MacNite/HiveHub/docs/hiveinside-ble-sensor.md

# HiveInside in-hive BLE sensor

**HiveInside** is an in-hive node that runs its vibration and acoustic FFTs on
board and broadcasts the finished results, so the HiveHub only has to scan for it
— no wiring into the hive. It supplies full FFT bands the wired sensors cannot,
and its temperature/humidity can replace the wired DS18B20/SHT4x for that hive.

HiveInside is the **XIAO nRF54LM20A Sense** node. It emits a 29-byte
manufacturer-data frame that a current HiveHub decodes out of the box:

| Board | How it is read | Advertising | OTA image |
|---|---|---|---|
| **HiveInside (nRF54LM20A)** | passive **beacon** scan (one shared window per cycle) | **always on**, no pairing window | signed Zephyr / MCUboot image (`zephyr.signed.bin`, a few hundred KB) |

> The earlier **ESP32-C6 HiveInside prototype** (which served the same frame over
> GATT and took a >1 MB ESP32 OTA image) has been **removed from the ecosystem**.
> HiveInside now unambiguously means the nRF54LM20A beacon node; there is no
> ESP32-C6 pairing type, GATT measurement path, or C6 firmware target anymore.

The frame carries (little-endian; valid only when the matching **flags** bit is
set — a failed on-board sensor is reported as *absent*, never as `0.0`):

| Group (flags bit) | Fields | HiveHub field |
|---|---|---|
| SHT (bit 0) | temperature, humidity | `hive_{n}_temp_c`, `ble_{n}_humidity_percent` |
| accel (bit 1) | RMS + peak + swarm/fanning/activity bands | `accel_{n}_*` (reused accelerometer fields; see the note on capture diagnostics below) |
| mic (bit 2) | RMS + peak + 5 acoustic bands | `hives[].mic.*`, read back as `mic_{n}_*` |
| battery (bit 3) | percent, millivolts | `ble_{n}_battery_percent`, `ble_{n}_battery_mv` |

The two broadband **peak** values (`accel_{n}_peak_mg`, `mic_{n}_peak_dbfs`)
arrived with **frame version 2** — appended after the version-1 fields, none of
which moved. HiveHub gates on the received frame length rather than the version
byte, so a node still on version 1 keeps decoding in full and simply reports no
peaks; the dashboard then falls back to the broadband RMS it always showed.

A [sample frame + reference decoder](../test-data/hiveinside_nrf54_beacon.py)
lives in `test-data/` (`python3 hiveinside_nrf54_beacon.py`).

Beyond the beacon, a HiveInside is the only device on a hub with a microphone
you can actually listen to: node firmware 0.6.2+ and hub firmware 0.30.0+ can
record 10–60 seconds from inside the hive on request and relay it here. That is
a connected, authenticated session rather than a passive scan, so it is covered
separately in [Listening to a hive](audio-recording.md).

---

## Pairing

1. **Firmware flag.** Set `ENABLE_BLE_SCAN 1` (the same shared passive scan used
   for HolyIot / RuuviTag). The nRF54 node is beacon-only, so no GATT measurement
   flag is needed. (`HIVEINSIDE_OTA_ENABLED`, default 1, compiles in the BLE OTA
   relay described below.)
2. **Pair from the setup portal.** Open the provisioning portal (press the setup
   button, or use **Start AP mode** in the dashboard, then join the
   `HiveHub-Setup-XXXX` AP), scan for BLE devices, and
   press **➕ Add BLE in-hive sensor** on the hive. Choose the sensor type
   **HiveInside (nRF54LM20A) — beacon** and enter/copy the node's MAC — picking
   the node from the scan dropdown selects the type for you. This is the hive's
   beacon lane, so it does not block a HiveTraffic bee counter or a HiveHeart on
   the same hive; it is exclusive only with the other beacon formats and with a
   wired DS18B20.

> The nRF54 node has **no pairing window** — it is always discoverable, so there
> is nothing to long-press before scanning. Its button just forces an immediate
> measurement.

The same choice is available in the
[web configurator](https://macnite.github.io/HiveHub/configurator.html), which
emits the matching `HIVE_i_JSON` pre-seed and firmware flags.

---

## Firmware updates (OTA relay)

The HiveHub is the only Wi-Fi node, so it **relays** a HiveInside image over BLE
GATT (streamed straight from the HTTPS download into the node's OTA
characteristics; the CRC-32 is verified end-to-end before the node swaps slots).
The relayed bytes are an nRF54 MCUboot image and are forwarded **opaquely** — the
HiveHub never runs its own ESP32 self-OTA architecture guard on them; only the
node verifies its own image. The relay locates the node by its identity address
(learned from this cycle's measurement scan) before connecting.

> The node advertises **connectable** (`ADV_IND`) continuously — it does not open
> an OTA window on demand, and this page previously said it was a
> "non-connectable beacon", which was never true of any shipped firmware. The
> measurement frame is still read passively out of the advertisement; being
> connectable is what lets the OTA relay and an audio session reach it at all.
> It also means the node's OTA GATT service is reachable by any BLE central in
> range, so the signing key MCUboot verifies against is the only thing standing
> between a stranger and the contents of slot 1 — build releases with your own
> key, not the SDK development key.

Uploads are **board-stamped** `nrf54lm20a` (the only HiveInside board). In the
dashboard firmware tool the target and version are filled in from the filename as
soon as the `.bin` is picked: HiveInside's build names its artifact
`hiveinside-nrf54lm20a-v0.4.7-lowpower.signed.bin` (see HiveInside's
[`docs/ota-over-ble.md`](https://github.com/MacNite/HiveInside/blob/main/docs/ota-over-ble.md)),
and the form reads `HiveInside` and `0.4.7` straight out of it — the build variant
(`bringup` / `lowpower`) and the `.signed` suffix are not part of the version. The
form says underneath the file picker what it recognized, and nothing is guessed for
a name it does not recognize: the target stays on whatever is selected and the
version field is left alone. The **Board** field then shows
`HiveInside (nRF54LM20A)` **disabled** — there is nothing to choose, and the
release is always stamped `nrf54lm20a`. The older
`hiveinside_nrf54lm20a_1.0.0.bin` naming is detected the same way. The
API still accepts an omitted board (legacy `board = NULL` releases), but the server
refuses a release whose declared board disagrees with its filename. A HiveInside release now
unambiguously means an nRF54 image, so no per-board matching is done — the latest
active HiveInside release (nrf54lm20a-stamped or a legacy board-agnostic one) is
relayed.

### Triggering a relay

Uploading a `.bin` only **registers** a release — nothing starts the transfer,
on any check-in. The relay is queued explicitly, either from the built-in
dashboard or over the API.

From the dashboard: **Device & admin → Firmware → HiveInside nodes**, then
**Relay to node** on the row for the hive you want to update. The button appears
only when the uploaded release would actually be accepted (see the guards
below), and requires an admin login.

The row then shows the relay's state — *relay queued*, *relaying…*, or *relay
failed* with the reason spelled out underneath (e.g. `HiveInside not found in
scan (asleep or out of range?)`). The button is disabled while a relay is
already queued or running, so a second click cannot stack a duplicate transfer.
A relay that succeeds leaves no badge: the node's advertised version changing is
the confirmation.

> Firmware downloads are deliberately excluded from response compression
> (`SelectiveGZipMiddleware`). A gzipped response has no `Content-Length`, and
> the ESP32 sizes its download from that header — compressing `/firmware/*` made
> every relay fail with `invalid firmware content length -1` before it opened a
> BLE session. Keep any reverse proxy in front of the API from re-compressing
> that path for the same reason.

Over the API:

```bash
curl -X POST -H "X-API-Key: $API_KEY" \
  "https://<host>/api/v1/devices/<device_id>/commands/update-hiveinside?slot=<hive>"
```

`slot` is the **hive index**, so any hive can be updated (up to `MAX_HIVES`), and
the HiveHub matches only HiveInside pairings when resolving the MAC. The relay
runs on the HiveHub's next upload cycle — about 10 minutes by default, or
whatever send interval the device is configured for. There is no separate
command poll; a command is picked up once per cycle, in every mode.

A relay that is claimed but never reported on (the HiveHub crashed, or simply
lost the fire-and-forget result POST after a multi-minute BLE transfer) is
swept back onto the queue after `STALE_CLAIM_MINUTES`, up to
`MAX_COMMAND_ATTEMPTS` times, and then failed with `timed out: claimed by the
device N time(s) without reporting a result`. Only relays are retried this way;
destructive commands such as `factory_reset` fail on the first timeout rather
than being silently repeated.

A hub that *resets* mid-relay no longer has to wait that out. It records the
command id in RTC memory before starting, and the next boot reports the attempt
explicitly — `hub reset during relay (panic/exception) — firmware transfer did
not complete` — against the still-open row. That closes the command on the first
cycle after the reset instead of an hour and three attempts later, and it names
the reset reason, so a crashing hub is distinguishable from one that is merely
out of range. The command is then genuinely failed rather than retried: re-queue
it yourself once the hub is healthy.

Two guards apply before the command is queued:

| Condition | Result |
|---|---|
| `slot` outside `1..18` | `400` |
| No active `hiveinside` release | `404` |
| Release not newer than the version the node advertises | `409` |

The version gate compares against `hives[].ble.firmware_version` — the version
the node itself broadcasts — so re-running the command after a successful update
is a no-op instead of a pointless multi-minute BLE transfer and a reboot of a
healthy hive sensor. A node that has never advertised a version is not gated.
Pass `force=true` to relay regardless, which is what you want after a reverted or
interrupted update where the node still runs the old image.

> **How the board/version are learned.** The nRF54 beacon advertises its board and
> firmware version in a second manufacturer-data element in its **scan response**
> (magic `'I'`), distinct from the 29-byte measurement frame (magic `'H'`). The
> HiveHub active-scans by default, so both arrive together — no GATT connection is
> needed to learn them, and the HiveHub forwards the node's `board`/`fw` fields to
> the backend.

> **nRF54 / MCUboot semantics:** the signed Zephyr image is small (transfer is
> quick), and after the relay completes the node reboots into a *test* image and
> confirms it. A reverted (unconfirmed) update silently keeps the old firmware,
> so verify the node's reported `fw` version after an update.

The dashboard shows that version in two places on **Device & admin**: the
**Status** card's *In-hive sensors* list (every paired wireless node, with the
version for the ones that advertise one — only HiveInside does), and
**Firmware → HiveInside nodes**: one row per hive whose node was heard, with the
advertised version and board (e.g. `v0.4.0 · nrf54lm20a`). The section only appears once a HiveInside
node has actually reported, and it keeps the last known identity when a node
misses a scan window, so it reads as "what this node is running", not "what was
in the last packet".

Each row in **Firmware → HiveInside nodes** is headed by the *hive* name, which
says where the node sits and nothing about which unit it is. The **?** beside
that name names the node itself: the local name it advertises and the BLE
address it is paired on. HiveInside firmware from **0.5.0** advertises
`HiveInside-XXXX`, where the four hex digits are the last two bytes of the
node's address — earlier firmware advertised a bare `HiveInside` on every node,
so for those the address is all there is to tell two of them apart. Both fields
ride in `hives[].ble.device_name` and `hives[].ble.mac` (raw JSON, no column),
and the HiveHub sends the address whether or not the node answered a scan.

### Diagnosing a failed relay

Watch the HiveHub's serial console at 115200 across an attempt. A healthy relay
prints, in order:

```
[CMD] Received command 20: update_hiveinside
[HI-OTA] Downloading HiveInside firmware: https://…/hiveinside-….signed.bin
[HEAP] relay-start: free=… largest=… min_ever=…
[HI-OTA] Download open: 1093632 bytes; bringing up BLE
[HEAP] relay-download-open: free=… largest=… min_ever=…
[HI-OTA] connecting to … 
[HI-OTA] connected: MTU=247 chunk=244 image=1093632 bytes crc=0x…
[HI-OTA] relayed 32768/1093632 bytes            ← every 32 KB
[HI-OTA] device reports DONE — it will reboot into the new image
[HI-OTA] result: OK
```

Where it stops, and what it says, maps to a cause:

* **`MTU=23 chunk=20`** — MTU negotiation did not take. The transfer still works
  but runs roughly ten times longer, which makes every other timeout tighter.
* **`DATA write failed …`** — the relay now asks the node *why* instead of
  guessing. `STATUS unreadable — link is down` is a genuine radio/link loss;
  `device rejected the stream: state=0x… (…)` means the node refused the bytes
  (CRC, size, flash write, wrong state) and the transfer never had a chance. The
  same distinction reaches the dashboard, so the row's reason is now the node's
  own verdict rather than "BLE link lost?" for all of them.
* **`… flash write failed (errno -116)`** — the trailing errno is the node's own
  `rc` from the failed flash operation, read from the seventh STATUS byte
  (HiveInside 0.4.7+, 0.24.13+ on this side). It exists because the `lowpower`
  HiveInside image has no console, so `state=0x12` was otherwise the entire
  diagnosis available in the field — and six error codes cannot separate a slot
  that is too small (`-EINVAL`) from a radio timeslot that never arrived
  (`-ETIMEDOUT`). Older nodes send six bytes and no suffix appears.
* **`[HEAP] *** CORRUPTION DETECTED at stage: … ***`** — the allocator's own
  structures are damaged. The named stage is the one that did it; everything
  after that point in the boot is unreliable, including any crash that follows.
* **`[BLE] … address type … known from this boot's scan`** — the normal path
  since 0.24.12. The relay reuses what the measurement scan already learned
  instead of running a second scan of its own; see the note below.
* **`[BLE] refusing to scan: the scan singleton belongs to port lifetime …`** —
  the safety net described below fired. Not a fault; the relay reports a clean
  failure rather than crashing.
* **A boot banner instead of a result line** — the hub reset mid-relay. Read
  `Reset reason:` on the line after the wake reason: `panic/exception` means a
  crash, with the Guru Meditation dump immediately above it.

A panic dump decodes in place when the console is `pio device monitor` (both
environments set `monitor_filters = esp32_exception_decoder`). For a dump
captured elsewhere, feed the addresses to `addr2line` against the exact image
that is flashed — `rename_firmware.py` names it `hivehub_<board>_<version>.elf`,
and `firmware/ci/package_build.sh` copies it into `firmware/dist/`:

```bash
riscv32-esp-elf-addr2line -pfiaC \
  -e firmware/dist/hivehub_esp32-c6_<version>.elf 0x… 0x… 0x…
```

The dump's trailing `ELF file SHA256:` must match that file, or the decoded
names are fiction.

> **Why the relay no longer scans (0.24.12+).** `NimBLEScan` initialises its
> scan-response timer once, in its constructor, against whichever porting layer
> is up at that moment. `NimBLEDevice::deinit()` tears the porting layer down
> *before* it would delete that singleton, so `deinit(true)` faults inside
> `~NimBLEScan()` — and `deinit(false)`, the workaround, leaves the singleton
> holding a callout belonging to a porting layer that no longer exists. Scan
> again later in the same boot and the first `ble_npl_callout_stop()` hands a
> freed handle to `esp_timer_stop()`: `Load access fault`, `MEPC` in
> `esp_timer.c:257`. That is exactly what killed a relay in the field — the
> measurement scan ran, the stack was cycled for the WiFi upload, and the
> relay's own 4-second locate scan ran in the second port lifetime.
>
> The relay now takes the address type from the measurement scan that already
> ran this cycle, so it never scans at all. `src/ble_stack.h` owns the stack's
> lifetime for every caller and refuses a scan that would land in the wrong port
> lifetime, so the remaining callers fail loudly instead of faulting.
>
> One consequence worth knowing: the setup portal's **discovery scan** is the
> one caller that legitimately wants to scan late in a boot. It declines with a
> log line instead of crashing — which, in 0.25.3, is what made a remotely
> opened AP list **no BLE devices at all** on any hub that already had a sensor
> paired: the AP came up, the radio was fine, and the scan simply never ran.
>
> Firmware **0.25.5** closes that (0.25.4 tried, but parked the request in a
> `RTC_DATA_ATTR` variable the bootloader wipes on the way back up): a `start_provisioning` command that would
> land in a spent port lifetime parks the request in RTC memory and reboots, so
> the portal opens before the first measurement cycle — where the scan is
> allowed — exactly as a button press does. Nothing is needed from the user
> beyond noticing the extra reboot. If a portal ever does come up without a
> scan, it now says so on the page instead of showing an empty list.

See [api.md](api.md) for the `update-hiveinside` command and payload.
