MacNite/HiveHub/docs/holyiot-ble-sensor.md

# HolyIot 25015 in-hive BLE sensor

HiveHub can read up to **two HolyIot 25015 BLE sensors** — one per hive — as
optional in-hive sensors. The ESP32 acts as a passive **BLE bridge**: no wiring
into the hive, just a battery beacon sitting on/near the comb that the logger
scans for once per upload cycle.

The 25015 (nRF54L15) carries three sensors:

| On-board chip | Measures | HiveHub field |
|---|---|---|
| SHT40 | temperature | `hive_{1,2}_temp_c` (shared with / replacing the wired DS18B20) |
| SHT40 | relative humidity | `ble_{1,2}_humidity_percent` |
| LPS22HB | barometric pressure | `ble_{1,2}_pressure_hpa` |
| LIS2DH12 | 3-axis acceleration | `accel_{1,2}_*` (reused accelerometer fields) |

It replaces the previous wired LIS3DH/LIS2DH12 accelerometer
([accelerometer.md](accelerometer.md)).

---

## Enabling and pairing

1. **Firmware flag.** Set `ENABLE_BLE_SCAN 1` in `secrets.h` (see
   `secrets.example.h` for all options). The wired in-hive microphone
   (`ENABLE_INMP441_MICS`) and DS18B20 probes (`ENABLE_DS18B20_HIVE_TEMP`) are
   independent optional features — turn them off if a build relies on the BLE
   sensor instead.
2. **Pair from the setup portal.** Open the provisioning portal (short-press the
   setup button, join the `HiveHub-Setup-XXXX` AP, browse to
   `http://192.168.4.1/`). Under **Wireless sensors**:
   - Click **scan for wireless sensors** to list advertising BLE devices; sensors
     carrying a parseable 25015 payload are flagged.
   - Click **➕ Add wireless sensor**, leave the type as an in-hive sensor
     (e.g. **HolyIot 25015**), pick **Hive 1** or **Hive 2** in the **Maps to**
     dropdown, paste the sensor's MAC, then **Save and reboot**. The **Maps to**
     choice — not the row order — decides the hive, so you can pair a wireless
     sensor for hive 2 alone and leave hive 1 on its wired probe.
   The MACs persist in Preferences (`ble_mac0` = hive 1, `ble_mac1` = hive 2).

Each cycle the firmware scans for `HOLYIOT_BLE_SCAN_SECONDS` (default 6 s),
matches advertisements to the paired MACs, and folds the readings into the
normal measurement upload before connecting WiFi.

### Hive temperature source

When `ENABLE_DS18B20_HIVE_TEMP` is on **and** the wired probe returns a valid
reading, the DS18B20 wins and the BLE temperature is the fallback. With the
DS18B20 disabled, `hive_{1,2}_temp_c` comes from the paired sensor's SHT40.

---

## Advertisement format — confirmed June 2026

The 25015 (HY-25015, P6-B Pro, firmware V1.0.0) broadcasts **four simultaneous
advertisement slots**, each cycling at ~500 ms. All use company ID `0xFFFF` in
the manufacturer-specific AD (type `0xFF`). The slot type is identified by the
**frame-type byte** at offset 2 (first byte after the 2-byte company ID):

| Frame | Type byte | Payload (offsets within manufacturer data) |
|---|---|---|
| T&H | `0x0A` | d[3..4] temp int16 BE /10 → °C; d[5..6] humidity uint16 BE /10 → %RH |
| Accel | `0x0B` | d[3..4] X int16 BE mg; d[5..6] Y int16 BE mg; d[7..8] Z int16 BE mg |
| Baro | `0x0C` | d[3..5] pressure uint24 BE Pa; ×0.01 → hPa |
| iBeacon | `0x02` | Static Major/Minor proximity identifiers — **no sensor data** |

Battery percentage comes from the **Service Data** (UUID `0x180A`, 9 bytes):
`[frame_type][MAC 6 B][TX power][battery %]` — last byte.

The firmware decoder (`firmware/src/ble_sensor.cpp`) merges all three sensor
frames into a single snapshot per scan cycle. All confirmed against real packet
captures (nRF Connect) with simultaneous live readings from the companion app.

---

## Acceleration & the low-rate pre-swarm insight

A passive beacon emits **periodic single-shot** acceleration samples, not a
high-rate stream, so the 8–30 Hz FFT swarm band the wired sensor produced cannot
be computed. Instead:

- The firmware reports a **per-cycle AC magnitude** (gravity removed) in the
  reused `accel_{1,2}_rms_mg` / `accel_{1,2}_peak_mg` fields
  (`accel_{1,2}_band_*_mg` stay null). Raw per-axis values, battery % and link
  RSSI are kept in `raw_json` (`ble_{1,2}_accel_*_mg`,
  `ble_{1,2}_battery_percent`, `ble_{1,2}_rssi_dbm`).
- The server runs `detect_lowrate_accel_swarm` (insights.py): it trends the
  **night-time mean** of `accel_{1,2}_rms_mg` and raises a lower-confidence
  `swarm` / `watch` alert (`swarm-ble-vibration-chN`) when in-hive movement
  climbs ≥ `LOWRATE_SWARM_RISE_MULT`× over its baseline. Rising comb excitation
  over several days can precede swarming (Bencsik/Ramsey). When real FFT-band
  data exists for a hive, this detector defers to the band detector to avoid a
  duplicate alert.

This is a coarser signal than research-grade comb vibrometry — the LIS2DH12's
noise floor limits it to detecting the louder, collective movement changes — but
it adds a genuine, no-wiring pre-swarm cue alongside the weight and temperature
rules.

---

## Database

Migration `008_holyiot_ble_sensor.sql` adds the four new columns
(`ble_{1,2}_humidity_percent`, `ble_{1,2}_pressure_hpa`). `init_db()` creates the
same columns on fresh deployments, and both are idempotent. Acceleration and
temperature reuse the existing `accel_{1,2}_*` and `hive_{1,2}_temp_c` columns.
