MacNite/HiveHub/firmware/include/hive_config.h

// hive_config.h — dynamic registry of up to MAX_HIVES hives and the sensors
// mapped to each one. Replaces the old fixed "hive 1 / hive 2" model.
//
// Each hive owns:
//   - one SCALE, backed by an HX711 (legacy pins), a NAU7802 I2C channel
//     (optionally behind a TCA9548A mux), or a paired beehivemonitoring.com
//     HiveScale GATT sensor;
//   - up to three in-hive BLE sensors, one per "lane" (see ble_lanes.h): one
//     beacon (HolyIot / RuuviTag / HiveInside), one HiveTraffic bee counter and
//     one HiveHeart. A wired DS18B20 temperature probe, addressed by its 1-Wire
//     ROM, occupies the beacon lane — probe and beacon both feed hives[].temp_c,
//     so a hive still takes one or the other, never both;
//
// The whole registry is persisted as one compact JSON blob per hive in NVS
// ("h0_cfg" .. "h17_cfg") plus a "hive_count" key, written by the provisioning
// portal (portal.cpp) and parsed back here at boot. Before that NVS key ever
// exists, a device instead seeds gHives from either up to MAX_HIVES HIVE_i_JSON
// secrets.h macros (same blob shape, see hive_config.cpp's seedHivesFromSecrets)
// or, absent those, migrates the legacy two-slot keys into a 2-hive registry —
// either way existing devices keep working without a portal visit.
#pragma once

#include <Arduino.h>
#include "config.h"
#include "ble_lanes.h"

namespace hivecfg {

// Which hardware drives a scale channel.
enum class ScaleBackend : uint8_t {
  None    = 0,
  HX711   = 1,   // legacy load-cell amp on a dedicated pin pair
  NAU7802 = 2,   // 24-bit I2C ADC (optionally behind a TCA9548A mux)
};

struct ScaleChannel {
  ScaleBackend backend = ScaleBackend::None;

  // HX711 backend: which of the two board HX711 instances (0 -> HX1_*, 1 -> HX2_*).
  uint8_t hxIndex = 0;

  // NAU7802 backend. The NAU7802's I2C address is FIXED at 0x2A (no
  // address-select pin), so it is not part of the configuration: the legacy
  // "addr" JSON field is parsed for backward compatibility, normalized to
  // NAU7802_I2C_ADDRESS (with a log when it differed) and no longer persisted
  // or presented as configurable.
  int8_t  muxChannel = -1;   // -1 = directly on the main bus; 0..7 behind the mux
  uint8_t adcChannel = 1;    // NAU7802 input mux: 1 -> CH1, 2 -> CH2

  // Calibration (raw -> kg), same convention as the HX711 path: kg = (raw-offset)/factor.
  long  offset = 0;
  float factor = -7050.0f;

  // Runtime-only (never persisted): set by validateRegistry() when this channel
  // is part of an invalid/conflicting topology (duplicate physical channel,
  // out-of-range mux/ADC, direct+muxed NAU7802 mix, implausible calibration).
  // A flagged channel is never operated — scalebus::readChannel() fails closed —
  // but the stored configuration is preserved so the portal can show and fix it.
  bool configError = false;

  bool valid() const { return backend != ScaleBackend::None && !configError; }
};

// One wireless pairing. `type` matches the portal vocabulary
// (holyiot|ruuvitag|hiveinside_nrf54|hiveheart|hivescale|beecounter). A `hivescale`
// pairing is a scale source; every other type is an in-hive BLE sensor, at most
// one per lane (blelanes::laneFor). `isGatt()` marks connection-based types that
// count against MAX_GATT_READS_PER_CYCLE.
struct BlePairing {
  String type;
  String mac;   // canonical "AA:BB:CC:DD:EE:FF"
  bool isGatt() const;
};

static const uint8_t MAX_SCALES_PER_HIVE = 1;
// One pairing per lane, so the ceilings come straight from ble_lanes.h: at most
// four stored pairings (a wireless HiveScale scale source + the three in-hive
// lanes), of which at most three are in-hive sensors. hiveFromJson() enforces
// this on every load AND on every portal save.
static const uint8_t MAX_BLE_PER_HIVE        = blelanes::LANE_COUNT;
static const uint8_t MAX_INHIVE_BLE_PER_HIVE = blelanes::INHIVE_LANE_COUNT;

struct Hive {
  uint8_t index = 0;          // 1..MAX_HIVES; 0 means "slot unused"
  String  name;

  uint8_t      scaleCount = 0;
  ScaleChannel scales[MAX_SCALES_PER_HIVE];

  bool    hasDsRom = false;   // a DS18B20 ROM is mapped to this hive
  uint8_t dsRom[8] = {0};     // 1-Wire ROM address

  uint8_t    bleCount = 0;
  BlePairing ble[MAX_BLE_PER_HIVE];

  bool used() const { return index >= 1; }
};

// The live registry. gHiveCount entries of gHives[] are populated (index 1..N).
extern Hive    gHives[MAX_HIVES];
extern uint8_t gHiveCount;

// Parse the NVS per-hive blobs (and hive_count) into gHives. When no blobs exist
// yet, migrate the legacy fixed-slot keys (scale offsets/factors, ble_mac0/1,
// wcount/wtypeN/wmacN/wslotN) into a two-hive registry so an upgraded device keeps
// working without re-provisioning. Always finishes with validateRegistry().
void loadHiveConfig();

// Authoritative validation of the loaded registry (runs on every load AND on
// every portal save — never rely on the portal page's dropdown behavior):
//   - duplicate or out-of-range hive indices  -> offending hives dropped;
//   - invalid mux (-1..7 only, no masking), invalid ADC channel (1/2), invalid
//     HX711 index, duplicate physical channels, direct+muxed NAU7802 mixes,
//     non-finite/implausible calibration factors -> offending channels get
//     configError set (never operated, preserved for correction in the portal);
//   - obsolete wired-BeeCounter "beecounter"-typed pairings without a BLE MAC
//     cannot exist (pairings are MAC-keyed), so nothing wired can activate.
// Every problem is logged with hive index + channel detail. Returns true when
// nothing had to be flagged or dropped.
bool validateRegistry();

// Serialize gHives back to NVS (used after a calibration writeback).
void saveHiveConfig();

// Serialize a single hive to its compact JSON blob string (used by the portal).
String hiveToJson(const Hive& h);
// Parse one hive blob into `out`; returns false on malformed input.
bool   hiveFromJson(const String& json, Hive& out);

// Convenience: total configured wired scale channels across all hives (<= MAX_SCALES).
uint8_t totalScaleChannels();

// MAC of the HiveInside node on the hive addressed by `slot`, or "" when that
// hive carries no HiveInside pairing. `slot` is the HIVE INDEX (1..MAX_HIVES),
// so every hive can be targeted by an OTA relay — not just the first two, which
// is all the legacy bleSensorMac0/1 globals could ever reach. A registry whose
// hives are not numbered 1..N falls back to registry position `slot - 1`, which
// is what the legacy globals addressed.
//
// Only HiveInside pairings are ever returned: the legacy globals held the first
// beacon of ANY type, so a hive whose first pairing was a HolyIot or RuuviTag
// pointed an OTA relay straight at the wrong device.
String hiveInsideMacForSlot(uint8_t slot);

// The paired HiveTraffic counter's MAC for hive index `slot`, or "" when that
// hive has no counter. Same index-then-position resolution as
// hiveInsideMacForSlot, matching only "beecounter" pairings. Used by the
// update_beecounter OTA relay; the measurement path walks the registry itself
// (bee_counter_client.cpp::bleRunCycleRegistry) rather than going slot by slot.
String beeCounterMacForSlot(uint8_t slot);

// Format/parse a DS18B20 ROM as 16 hex chars ("28FF64...") for the portal/NVS.
String   romToHex(const uint8_t rom[8]);
bool     romFromHex(const String& hex, uint8_t rom[8]);

}  // namespace hivecfg
