MacNite/HiveHub/firmware/include/bee_counter_client.h

// bee_counter_client.h — HiveTraffic entrance bee counter, BLE/GATT ONLY.
//
// The wired I2C BeeCounter path (its fixed slave addresses, register map,
// latch/reset command, snapshot retries, and firmware-over-the-wire updates)
// was removed: BLE/GATT is the only supported BeeCounter transport. Once per
// upload cycle the firmware connects
// to each paired HiveTraffic MAC, reads one JSON measurement characteristic —
// LIFETIME totals only — and disconnects. The backend differences consecutive
// totals into per-interval counts, so no latch/reset command exists.
//
// Firmware updates run over GATT as well: the backend queues an
// `update_beecounter` command and HiveHub streams the image into the counter's
// OTA characteristics (see gatt_ota.h and hivehub_network.cpp). That path is
// entirely separate from the measurement read below — it opens its own session
// and shares nothing but the service UUID.

#pragma once

#include <Arduino.h>
#include <ArduinoJson.h>
#include "config.h"   // ENABLE_WIRELESS_BEECOUNTER + BEECOUNTER_GATT_* UUIDs

namespace beecnt {

// One totals-only reading from a HiveTraffic counter, taken each upload cycle.
// Field names mirror the HiveTraffic measurement JSON (docs/ble-mode.md in the
// 2026-easy-bee-counter repo), normalized across wire revisions — see
// bee_counter_wire.h, which owns the fw:2 / fw:3 branch and the decoding.
struct Snapshot {
    bool     present          = false;  // device connected and parsed this cycle
    uint8_t  fw_version       = 0;      // wire-protocol revision ("fw")
    // Image version ("ver", e.g. "0.1.0"), empty when the counter runs firmware
    // older than the field. NOT the same thing as fw_version above: that one
    // versions the wire format and does not move when the firmware does. This
    // is what the backend gates an OTA relay on and what confirms, after the
    // counter reboots, that the update actually took. Fixed buffer rather than
    // a String: Snapshot is used as a MAX_HIVES-sized stack array.
    //
    // Because it is a char[] and the array is a stack local, anything putting it
    // into a JsonDocument must copy it (writeSnapshotToHive wraps it in
    // String()): ArduinoJson links a const char* by pointer, and the document
    // outlives this struct.
    char     version[16]      = {0};
    // Local name the counter reports ("name"), e.g. "HiveTraffic-8A3F". With the
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
